watterott/WebRadio/hardware/v2/main_bot.pdf

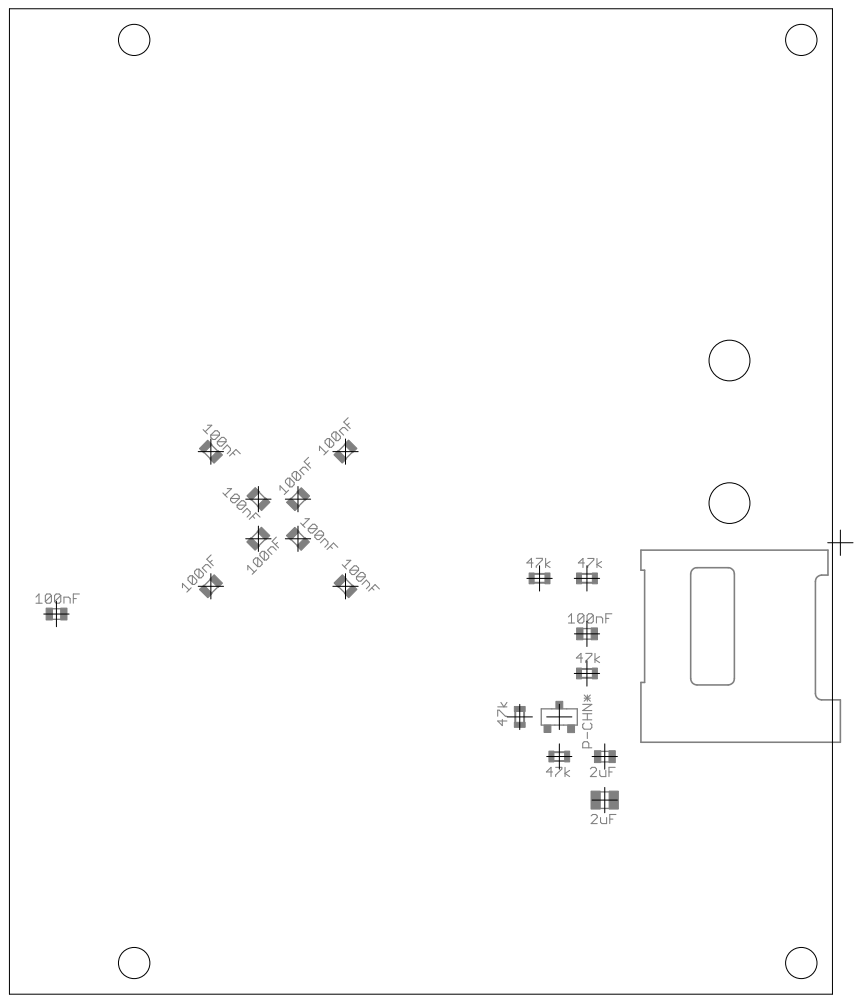
[picture p41: page 1]
