watterott/WebRadio/hardware/v2/main_top.pdf

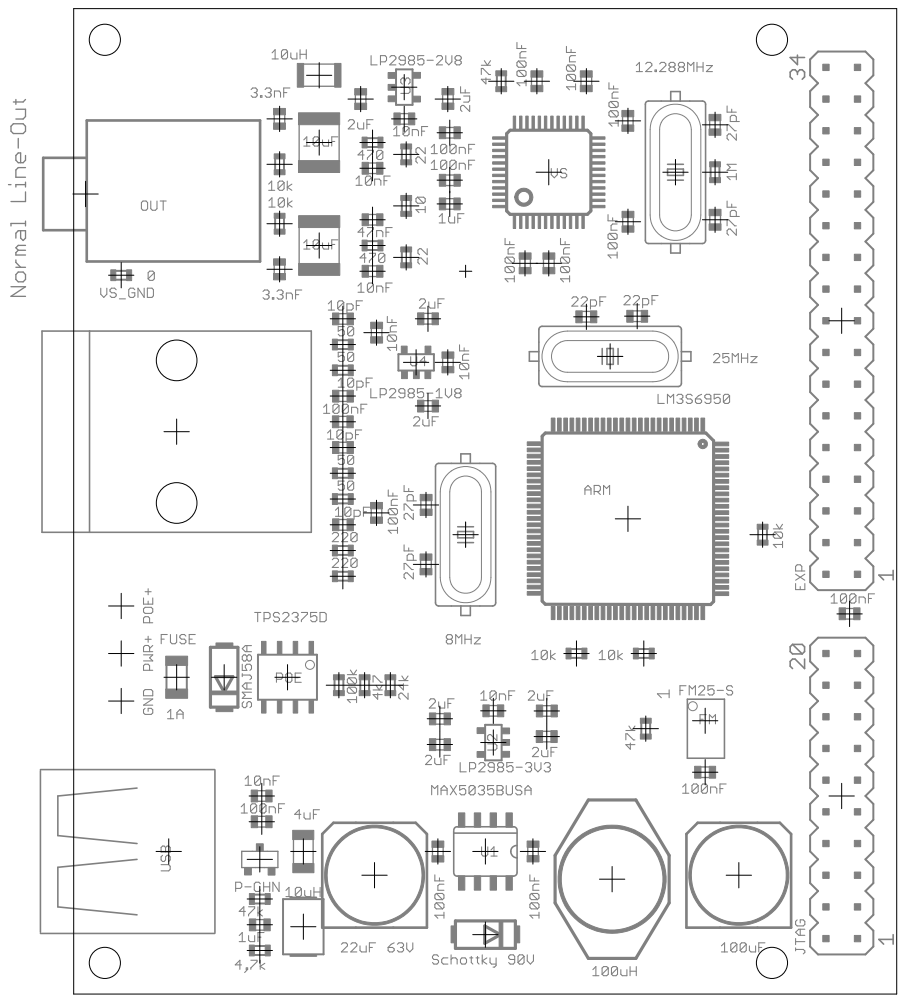
[picture p42: page 1]
