watterott/WebRadio/software/alarm.h

#ifndef _ALARM_H_
#define _ALARM_H_


//----- DEFINES -----
#define ALARMTIMES                     (8)
#define ALARM_FILE                     "ALARM.INI"
#define ALARM_FILEITEMS                (3)


typedef struct
{
  unsigned int wdays;  //Bit0=Sunday, Bit1=Monday, Bit2=Tueday...
  unsigned int h;
  unsigned int m;
  unsigned int action; //0=nothing, 1=play, 2=standby
} ALARMTIME;


//----- PROTOTYPES -----
unsigned int                           alarm_check(TIME *time);
unsigned int                           alarm_getfile(char *dst, unsigned int nr);
unsigned int                           alarm_getvol(void);
unsigned int                           alarm_settime(unsigned int item, ALARMTIME *time);
unsigned int                           alarm_gettime(unsigned int item, ALARMTIME *time);
unsigned int                           alarm_parsetime(const char *src, ALARMTIME *time);
void                                   alarm_load(void);
unsigned int                           alarm_openitem(unsigned int item);
void                                   alarm_getitem(unsigned int item, char *name);
unsigned int                           alarm_items(void);
void                                   alarm_init(void);


#endif //_ALARM_H_
