watterott/WebRadio/software/io.h

#ifndef _IO_H_
#define _IO_H_


//----- DEFINES -----
//CPU Freq.
// 50.0 MHz - SYSCTL_SYSDIV_4
// 40.0 MHz - SYSCTL_SYSDIV_5
// 33.3 MHz - SYSCTL_SYSDIV_6
// 28.6 MHz - SYSCTL_SYSDIV_7
// 25.0 MHz - SYSCTL_SYSDIV_8
// 22.2 MHz - SYSCTL_SYSDIV_9
// 20.0 MHz - SYSCTL_SYSDIV_10
#define LM3S_SYSDIV                    SYSCTL_SYSDIV_6

//LM3S6950 Revision: LM3S_REV_A1, LM3S_REV_A2 or LM3S_REV_B0
#define LM3S_REV_A2

//Display: LCD_L2F50, LCD_LPH88, LCD_LS020, LCD_MIO283QT1, LCD_MIO283QT2
#define LCD_LPH88
//#define LCD_MIRROR                     //mirror display
//#define LCD_ROTATE                     //rotate display (90 degree)
#define LCD_PWMFREQ                    (60000) //60000 Hz LED PWM Freq
#define LCD_PWMMIN                     (5)     // 5 % (1...100%)
#define LCD_PWMSTANDBY                 (15)    //15 % (1...100%)

//Standby
#define STANDBY_TIME                   (3*60)  //standby after x seconds

//SSI Speed: LCD, SD, F-RAM, VS
#define SSI_SPEED                      (8000000UL) //8 MHz (max ssi speed)

//Rotary Encoder switch times
#define SW_SHORTTIME                   (8)   //  8*10ms =   80ms
#define SW_LONGTIME                    (120) //120*10ms = 1200ms

//IR
#define IR_BITTIME                     (1778) //1.778 ms
#define IR_MAXERR                      (150)  //150 us (max. half bit time error)
#define IR_DETECT                      (0)
#define IR_STARTBIT1                   (1)
#define IR_STARTBIT2                   (2)
#define IR_DATABIT                     (3)
#define IR_TV1                         (0)
#define IR_TV2                         (1)
#define IR_VCR1                        (5)
#define IR_VCR2                        (6)
#define IR_ALLADDR                     (0x1F)

//IR and Rotary Encoder Commandos
#define SW_PRESSED                     (1)
#define SW_PRESSEDLONG                 (2)
#define SW_VOLP                        (3)
#define SW_VOLM                        (4)
#define SW_UP                          (5)
#define SW_DOWN                        (6)
#define SW_ENTER                       (7)
#define SW_POWER                       (8)

//FM
#define FM_WREN                        (0x06) //Set Write Enable Latch
#define FM_WRDI                        (0x04) //Write Disable
#define FM_RDSR                        (0x05) //Read Status Register
#define FM_WRSR                        (0x01) //Write Status Register
#define FM_READ                        (0x03) //Read Memory Data
#define FM_FSTRD                       (0x0B) //Fast Read Memory Data
#define FM_WRITE                       (0x02) //Write Memory Data
#define FM_SLEEP                       (0xB9) //Enter Sleep Mode
#define FM_RDID                        (0x9F) //Read Device ID
#define FM_SNR                         (0xC3) //Read S/N 

//Check hardware config
#if defined LM3S_REV_A1                //LM3S Rev
# define LM3S_NAME "LM3S-A1"
#elif defined LM3S_REV_A2
# define LM3S_NAME "LM3S-A2"
#elif defined LM3S_REV_B0
# define LM3S_NAME "LM3S-B0"
#else
# warning "LM3S Rev not defined"
#endif
#if defined LCD_L2F50                  //LCD
# define LCD_NAME "S65-L2F50"
#elif defined LCD_LPH88
# define LCD_NAME "S65-LPH88"
#elif defined LCD_LS020
# define LCD_NAME "S65-LS020"
#elif defined LCD_MIO283QT1
# define LCD_NAME "MIO283QT1"
#elif defined LCD_MIO283QT2
# define LCD_NAME "MIO283QT2"
#else
# warning "LCD not defined"
#endif

//--- Pins ---
//Encoder
#define ENC_PHA_READ()                 GPIOPinRead(GPIO_PORTD_BASE, GPIO_PIN_1)
#define ENC_PHB_READ()                 GPIOPinRead(GPIO_PORTF_BASE, GPIO_PIN_0)
#define ENC_SW_READ()                  GPIOPinRead(GPIO_PORTE_BASE, GPIO_PIN_4)
//IR
#define IR_READ()                      GPIOPinRead(GPIO_PORTD_BASE, GPIO_PIN_2)
//LCD
#define LCD_RST_DISABLE()              GPIOPinWrite(GPIO_PORTB_BASE, GPIO_PIN_5, GPIO_PIN_5)
#define LCD_RST_ENABLE()               GPIOPinWrite(GPIO_PORTB_BASE, GPIO_PIN_5, 0)
#define LCD_CS_DISABLE()               GPIOPinWrite(GPIO_PORTB_BASE, GPIO_PIN_6, GPIO_PIN_6)
#define LCD_CS_ENABLE()                GPIOPinWrite(GPIO_PORTB_BASE, GPIO_PIN_6, 0)
#define LCD_RS_DISABLE()               GPIOPinWrite(GPIO_PORTB_BASE, GPIO_PIN_4, GPIO_PIN_4)
#define LCD_RS_ENABLE()                GPIOPinWrite(GPIO_PORTB_BASE, GPIO_PIN_4, 0)
//SD
#define MMC_POWERON()                  GPIOPinWrite(GPIO_PORTB_BASE, GPIO_PIN_0, 0); \
                                       GPIOPadConfigSet(GPIO_PORTB_BASE, GPIO_PIN_0, GPIO_STRENGTH_4MA, GPIO_PIN_TYPE_STD)
#define MMC_POWEROFF()                 GPIOPinWrite(GPIO_PORTB_BASE, GPIO_PIN_0, GPIO_PIN_0); \
                                       GPIOPadConfigSet(GPIO_PORTB_BASE, GPIO_PIN_0, GPIO_STRENGTH_2MA, GPIO_PIN_TYPE_STD_WPU)
#define MMC_SELECT()                   GPIOPinWrite(GPIO_PORTB_BASE, GPIO_PIN_1, 0)
#define MMC_DESELECT()                 GPIOPinWrite(GPIO_PORTB_BASE, GPIO_PIN_1, GPIO_PIN_1)
#define MMC_SCK_LOW()                  GPIOPinWrite(GPIO_PORTE_BASE, GPIO_PIN_0, 0)
#define MMC_SCK_HIGH()                 GPIOPinWrite(GPIO_PORTE_BASE, GPIO_PIN_0, GPIO_PIN_0)
#define MMC_SI_LOW()                   GPIOPinWrite(GPIO_PORTE_BASE, GPIO_PIN_3, 0)
#define MMC_SI_HIGH()                  GPIOPinWrite(GPIO_PORTE_BASE, GPIO_PIN_3, GPIO_PIN_3)
//VS
#define VS_DREQ_READ()                 GPIOPinRead(GPIO_PORTA_BASE, GPIO_PIN_1)
#define VS_RST_DISABLE()               GPIOPinWrite(GPIO_PORTA_BASE, GPIO_PIN_7, GPIO_PIN_7)
#define VS_RST_ENABLE()                GPIOPinWrite(GPIO_PORTA_BASE, GPIO_PIN_7, 0)
#define VS_CS_DISABLE()                GPIOPinWrite(GPIO_PORTA_BASE, GPIO_PIN_6, GPIO_PIN_6)
#define VS_CS_ENABLE()                 GPIOPinWrite(GPIO_PORTA_BASE, GPIO_PIN_6, 0)
#define VS_DCS_DISABLE()               GPIOPinWrite(GPIO_PORTA_BASE, GPIO_PIN_3, GPIO_PIN_3)
#define VS_DCS_ENABLE()                GPIOPinWrite(GPIO_PORTA_BASE, GPIO_PIN_3, 0)
//USB Power
#define USB_ON()                       GPIOPinTypeGPIOOutputOD(GPIO_PORTF_BASE, GPIO_PIN_1); \
                                       GPIOPinWrite(GPIO_PORTF_BASE, GPIO_PIN_1, 0); \
                                       GPIOPadConfigSet(GPIO_PORTF_BASE, GPIO_PIN_1, GPIO_STRENGTH_4MA, GPIO_PIN_TYPE_OD); \
                                       delay_ms(400)
#define USB_OFF()                      GPIOPinWrite(GPIO_PORTF_BASE, GPIO_PIN_1, GPIO_PIN_1); \
                                       GPIOPinTypeGPIOInput(GPIO_PORTF_BASE, GPIO_PIN_1); \
                                       GPIOPadConfigSet(GPIO_PORTF_BASE, GPIO_PIN_1, GPIO_STRENGTH_2MA, GPIO_PIN_TYPE_STD); \
                                       delay_ms(10)
//FM
#define FM_CS_DISABLE()                GPIOPinWrite(GPIO_PORTE_BASE, GPIO_PIN_1, GPIO_PIN_1)
#define FM_CS_ENABLE()                 GPIOPinWrite(GPIO_PORTE_BASE, GPIO_PIN_1, 0)


//----- PROTOTYPES -----
#ifndef LOADER
void                                   ethernet_setmac(uint64_t mac);
unsigned int                           ethernet_link(void);
unsigned int                           ethernet_data(void);
unsigned int                           ethernet_put(unsigned char *pkt, unsigned int len);
unsigned int                           ethernet_get(unsigned char *pkt, unsigned int len);
void                                   ethernet_handler(void);

void                                   vs_ssi_wait(void);
void                                   vs_ssi_writewait(void);
void                                   vs_ssi_write(unsigned char c);
unsigned char                          vs_ssi_readwrite(unsigned char c);
void                                   vs_ssi_speed(unsigned long speed);

void                                   fm_gets(unsigned char *s, unsigned long len);
void                                   fm_puts(const unsigned char *s, unsigned long len);
unsigned long                          fm_size(void);
unsigned long                          fm_free(void);
unsigned long                          fm_len(void);
void                                   fm_reset(void);
unsigned long                          fm_init(void);
#endif //LOADER

void                                   ssi_wait(void);
void                                   ssi_write(unsigned char c);
unsigned char                          ssi_readwrite(unsigned char c);
void                                   ssi_speed(unsigned long speed);
void                                   ssi_off(void);
void                                   ssi_on(void);

void                                   pwm_led(unsigned int power);

#ifndef LOADER
int                                    ir_cmd(void);
int                                    ir_rawdata(void);
void                                   ir_timer(void);
void                                   ir_edge(void);

unsigned int                           ir_getkeyvolm(void);
unsigned int                           ir_getkeyvolp(void);
unsigned int                           ir_getkeyok(void);
unsigned int                           ir_getkeydown(void);
unsigned int                           ir_getkeyup(void);
unsigned int                           ir_getkeypower(void);

void                                   ir_setkeyvolm(unsigned int key);
void                                   ir_setkeyvolp(unsigned int key);
void                                   ir_setkeyok(unsigned int key);
void                                   ir_setkeydown(unsigned int key);
void                                   ir_setkeyup(unsigned int key);
void                                   ir_setkeypower(unsigned int key);

unsigned int                           ir_getaddr(void);
void                                   ir_setaddr(unsigned int addr);
void                                   ir_init(void);
#endif //LOADER

int                                    keys_steps(void);
int                                    keys_sw(void);
void                                   keys_timerservice(void);

void                                   cpu_speed(unsigned int low_speed);
void                                   cpu_reset(void);
void                                   init_bor(unsigned int on);
void                                   init_periph(void);
void                                   init_pins(void);

void                                   delay_ms(unsigned long ms);

void                                   GPIOSetOutputOD(unsigned long port, unsigned char pins);
void                                   GPIOSetOutput(unsigned long port, unsigned char pins);
void                                   GPIOSetInput(unsigned long port, unsigned char pins);


#endif //_IO_H_
