watterott/WebRadio/software/vs_patch.c

#include "vs_patch.h"


//VS1033C: WMA Resync Patch + AAC DRC disable patch 1.1 (2008-02-20)
const unsigned short vs1033c_patch[VS1033C_PATCHLEN] =
{
  0x0007, 0x0001, 0x800c, 0x0006, 0x0002, 0x2800, 0xb000, 0x0007, /*    0 */
  0x0001, 0x82c0, 0x0006, 0x0028, 0xf400, 0x4215, 0x2900, 0xc1c0, /*    8 */
  0x0000, 0x0024, 0x3600, 0x0024, 0x4090, 0x4548, 0x0000, 0x0024, /*   10 */
  0x2000, 0x0015, 0xb080, 0x0024, 0x0006, 0x8f17, 0x3f13, 0xfc0e, /*   18 */
  0x3f03, 0x4024, 0x0020, 0xa50f, 0x0000, 0x004d, 0x2000, 0x0000, /*   20 */
  0x0000, 0xb3ce, 0x0006, 0x8f17, 0x3713, 0xdc0e, 0x3703, 0x4024, /*   28 */
  0x2800, 0xb500, 0x0020, 0xa548, 0x0007, 0x0001, 0x821c, 0x0006, /*   30 */
  0x0026, 0x3613, 0x0024, 0x3e00, 0x3802, 0x0030, 0x0257, 0x3700, /*   38 */
  0x0024, 0x0013, 0x4d02, 0xd024, 0x0024, 0x0010, 0x5102, 0x2800, /*   40 */
  0x8a85, 0xd024, 0x0024, 0x0010, 0x5502, 0x2800, 0x8a85, 0xd024, /*   48 */
  0x0024, 0x0000, 0x0024, 0x2800, 0x8b55, 0x0000, 0x0002, 0x0007, /*   50 */
  0x0557, 0x3009, 0x3c02, 0x2000, 0x0000, 0x36f0, 0x1802, 0x0007, /*   58 */
  0x0001, 0x8000, 0x0006, 0x0002, 0x2800, 0x8700, 0x0007, 0x0001, /*   60 */
  0x82d4, 0x0006, 0x0066, 0x3613, 0x0024, 0x3e22, 0xb815, 0x3e05, /*   68 */
  0xb814, 0x3615, 0x0024, 0x0000, 0x800a, 0x3e10, 0x3801, 0x3e10, /*   70 */
  0xb803, 0x3e11, 0x3805, 0x3e11, 0xb807, 0x3e04, 0x3811, 0x0006, /*   78 */
  0x6950, 0x3010, 0x0024, 0x3010, 0x4024, 0x4cc2, 0x0044, 0x30d1, /*   80 */
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
  0x0000, 0x291f, 0xc6c0, 0x0002, 0x4f88, 0x30e1, 0x184c, 0x3000, /* 10f8 */
  0x0024, 0x6012, 0x0024, 0x0008, 0x0001, 0x2802, 0x4015, 0x0000, /* 1100 */
  0x0024, 0x6498, 0x0024, 0x3e10, 0x4024, 0x0000, 0x0081, 0x2901, /* 1108 */
  0x3140, 0x3e01, 0x0024, 0x36e3, 0x004c, 0x3000, 0x0024, 0x6012, /* 1110 */
  0x0024, 0x000b, 0x8011, 0x2802, 0x4c55, 0x0006, 0x8112, 0x0000, /* 1118 */
  0x0201, 0x0004, 0x0010, 0x2915, 0x8300, 0x0001, 0x0000, 0x000b, /* 1120 */
  0x8011, 0x0005, 0x0010, 0x291f, 0xc6c0, 0x0001, 0x0000, 0x0006, /* 1128 */
  0x8110, 0x30e1, 0x0024, 0x3000, 0x0024, 0x6012, 0x0024, 0x0000, /* 1130 */
  0x0281, 0x2802, 0x4745, 0x6012, 0x0024, 0x000b, 0x8001, 0x2802, /* 1138 */
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
};
