watterott/WebRadio/software/eth/dhcp.h

#ifndef _DHCP_H_
#define _DHCP_H_


//----- DEFINES -----
#define DHCPSERVER_PORT                (67)
#define DHCPCLIENT_PORT                (68)

#define DHCP_TIMEOUT                   (2) //seconds

#define DHCP_CLOSED                    (0)
#define DHCP_DISCOVER                  (1)
#define DHCP_REQUEST                   (2)
#define DHCP_ACK                       (3)

//Proto: DHCP (Dynamic Host Configuration Protocol)
#define DHCP_OFFSET                    (ETH_HEADERLEN+IP_HEADERLEN+UDP_HEADERLEN)
#define DHCP_HEADERLEN                 (44+64+128)
#define DHCP_OP_REQUEST                (1)
#define DHCP_OP_REPLY                  (2)
#define DHCP_HTYPE_ETH                 (1)
#define DHCP_HLEN_MAC                  (6)
#define DHCP_MCOOKIE                   (0x63825363)
#define DHCP_OPTION_NETMASK            (1)
#define DHCP_OPTION_ROUTER             (3)
#define DHCP_OPTION_TIMESERVER         (4)
#define DHCP_OPTION_DNS                (6)
#define DHCP_OPTION_HOSTNAME           (12)
#define DHCP_OPTION_REQUESTEDIP        (50)
#define DHCP_OPTION_MSGTYPE            (53)
# define DHCP_MSG_DISCOVER             (1)
# define DHCP_MSG_OFFER                (2)
# define DHCP_MSG_REQUEST              (3)
# define DHCP_MSG_DECLINE              (4)
# define DHCP_MSG_ACK                  (5)
# define DHCP_MSG_NAK                  (6)
# define DHCP_MSG_RELEASE              (7)
#define DHCP_OPTION_SERVERID           (54)
#define DHCP_OPTION_PARAMLIST          (55)
#define DHCP_OPTION_CLIENTID           (61)
#define DHCP_OPTION_SMTPSERVER         (69)
#define DHCP_OPTION_POP3SERVER         (70)
typedef struct __attribute__((packed))
{
  unsigned int     op        :  8; // 8bit OP
  unsigned int     htype     :  8; // 8bit HType
  unsigned int     hlen      :  8; // 8bit HLen
  unsigned int     hops      :  8; // 8bit HOPS
  unsigned long    xid       : 32; //32bit ID
  unsigned int     secs      : 16; //16bit Seconds
  unsigned int     flags     : 16; //16bit Flags
  unsigned long    ciaddr    : 32; //32bit Client IP
  unsigned long    yiaddr    : 32; //32bit Your IP
  unsigned long    siaddr    : 32; //32bit Server IP
  unsigned long    giaddr    : 32; //32bit Relay-Agent IP
  union
  {
    uint64_t       mac       : 48; //48bit Client MAC
    uint8_t        addr[16];       //16byte MAC
  } chaddr;
  uint8_t          sname[64];      //64byte Server name
  uint8_t          file[128];      //128byte File
  unsigned long    mcookie   : 32; //32bit Magic Cookie: 0x63825363
  uint8_t          options[312-4]; //312byte Options (includes Magic Cookie)
} DHCP_Header;


//----- PROTOTYPES -----
unsigned int                           dhcp_request(unsigned int idx, unsigned int msg);
unsigned int                           dhcp_getcfg(void);
void                                   dhcp_udpapp(unsigned int idx, const unsigned char *rx, unsigned int rx_len, unsigned char *tx);


#endif //_DHCP_H_
