watterott/WebRadio/software/eth/ntp.c

#include <stdint.h>
#include <stdlib.h>
#include <stdio.h>
#include <string.h>
#include <ctype.h>
#include "../debug.h"
#include "../tools.h"
#include "../main.h"
#include "../eth.h"
#include "utils.h"
#include "ntp.h"


volatile unsigned long ntp_time=0UL;


unsigned int ntp_request(unsigned int idx)
{
  MAC_Addr mac;
  NTP_Header *tx_ntp;

  mac = arp_getmac(eth_getntp());

  tx_ntp = (NTP_Header*) &eth_txbuf[NTP_OFFSET];

  memset(tx_ntp, 0, NTP_HEADERLEN);

  tx_ntp->flags = (0<<6)|(1<<3)|(3<<0); //LI=0 | VN=1 | Mode=3 -> Client

  idx = udp_open(idx, mac, eth_getntp(), NTP_PORT, NTP_PORT, 0, NTP_HEADERLEN);

  return idx;
}


unsigned long ntp_gettime(void)
{
  long timeout, timeout_ntp;
  unsigned int idx;

  ntp_time = 0UL;

  idx = ntp_request(UDP_ENTRIES);

  if(idx < UDP_ENTRIES)
  {
    timeout     = getontime()+ETH_TIMEOUT;
    timeout_ntp = getontime()+NTP_TIMEOUT;
    for(;;)
    {
      eth_service();
  
      if(ntp_time != 0UL)
      {
        break;
      }
      if(getdeltatime(timeout_ntp) > 0)
      {
        timeout_ntp = getontime()+NTP_TIMEOUT;
        idx = ntp_request(idx);
      }
      if(getdeltatime(timeout) > 0)
      {
        break;
      }
    }
  
    udp_close(idx);
  }

  return ntp_time;
}


void ntp_udpapp(unsigned int idx, const unsigned char *rx, unsigned int rx_len, unsigned char *tx)
{
  const NTP_Header *rx_ntp;
  unsigned long time;

  DEBUGOUT("NTP: UDP app\n");
  
  rx_ntp = (const NTP_Header*) rx;

  if((rx_ntp->flags&0x07) == 4) //Mode=4 -> Server
  {
    time  = swap32(rx_ntp->trn_ts);
    time -= 2208988800UL; //seconds: 1900-1970
    time += eth_gettimediff();
    if(eth_getsummer()) //summer time
    {
      time += 3600; //add one hour
    }
    ntp_time = time;
  }

  return;
}
