watterott/WebRadio/software/eth/shoutcast.h

#ifndef _SHOUTCAST_H_
#define _SHOUTCAST_H_


//----- DEFINES -----
#define SHOUTCAST_SERVERPORT           (80)
#define SHOUTCAST_CLIENTPORT1          (1001)
#define SHOUTCAST_CLIENTPORT2          (1002)
#define SHOUTCAST_CLIENTPORT3          (1003)

#define SHOUTCAST_TIMEOUT              (15) //s
#define SHOUTCAST_TRY                  (3)  //times

#define SHOUTCAST_CLOSED               (0)
#define SHOUTCAST_CLOSE                (1)
#define SHOUTCAST_OPENED               (2)
#define SHOUTCAST_HEADER               (3)
#define SHOUTCAST_OPEN                 (4)
#define SHOUTCAST_ADDRMOVED            (5)
#define SHOUTCAST_SERVERFULL           (6)
#define SHOUTCAST_ERROR                (7)
#define SHOUTCAST_ERRTIMEOUT           (8)


//----- PROTOTYPES -----
void                                   shoutcast_close(void);
unsigned int                           shoutcast_open(void);
void                                   shoutcast_putogg(const unsigned char *s, unsigned int len);
void                                   shoutcast_putdata(const unsigned char *s, unsigned int len);
void                                   shoutcast_tcpapp(unsigned int idx, const unsigned char *rx, unsigned int rx_len, unsigned char *tx);


#endif //_SHOUTCAST_H_
