watterott/WebRadio/software/vs_patch.h

#ifndef _VS_PATCH_H_
#define _VS_PATCH_H_


//----- DEFINES -----
#define VS1033C_PATCHLEN               (288)
#define VS1033D_PATCHLEN               (142)
#define VS1053B_PATCHLEN               (6714)


//----- GLOBALS -----
extern const unsigned short vs1033c_patch[];
extern const unsigned short vs1033d_patch[];
extern const unsigned short vs1053b_patch[];


#endif //_VS_PATCH_H_
