watterott/WebRadio/software/tools.h

#ifndef _TOOLS_H_
#define _TOOLS_H_


//----- DEFINES -----
typedef struct
{
  unsigned int s;     //0-59
  unsigned int m;     //0-59
  unsigned int h;     //0-23
  unsigned int day;   //1-31
  unsigned int month; //1-12
  unsigned int year;  //1970-...
  unsigned int wday;  //0-6 (0=Sunday)
} TIME;


//----- PROTOTYPES -----
void                                   strshrinkpath(char *path);
char*                                  strrmvspace(char *dst, const char *src);
char*                                  strtoupper(char *dst, const char *src);
int                                    strstrk(char *dst, const char *src, const char *key);
const char*                            strstri(const char *s, const char *pattern);
#ifndef strncmpi
# define TOOLS_STRNCMPI
int                                    strncmpi(const char *s1, const char *s2, size_t n);
#endif

#ifndef itoa
//# define TOOLS_ITOA
char*                                  itoa(int val, char *buf, int radix);
#endif

#ifndef utoa
//# define TOOLS_UTOA
char*                                  utoa(unsigned val, char *buf, int radix);
#endif

#ifndef ltoa
//# define TOOLS_LTOA
char*                                  ltoa(long val, char *buf, int radix);
#endif

#ifndef ultoa
//# define TOOLS_ULTOA
char*                                  ultoa(unsigned long val, char *buf, int radix);
#endif

unsigned int                           atou_hex(const char *s);
unsigned int                           atou(const char *s);
unsigned int                           atorgb(const char *s);

void                                   sectotime(unsigned long s, TIME *t);
unsigned long                          timetosec(unsigned int s, unsigned int m, unsigned int h, unsigned int day, unsigned int month, unsigned int year);
void                                   daytime(char *s, TIME *t);


#endif //_TOOLS_H_
